KatherineSandys/mini_project_ECE362/inc/f16.h

#ifndef F16
#define F16
const char f16_map[] = {
		0xfe, 0xfe, 0xfe, 0xff, 	/*Color of index 0*/
		  0x12, 0x27, 0xfd, 0xff, 	/*Color of index 1*/
		  0x00, 0x00, 0x01, 0xff, 	/*Color of index 2*/
		  0x03, 0xaa, 0xf9, 0xff, 	/*Color of index 3*/
		  0x09, 0x53, 0xfb, 0xff, 	/*Color of index 4*/
		  0x17, 0x42, 0x4a, 0xff, 	/*Color of index 5*/
		  0x34, 0xfd, 0xfd, 0xff, 	/*Color of index 6*/
		  0x2d, 0xe8, 0xd0, 0xff, 	/*Color of index 7*/
		  0x33, 0xaf, 0x67, 0xff, 	/*Color of index 8*/
		  0xcd, 0x90, 0x04, 0xff, 	/*Color of index 9*/
		  0x71, 0x59, 0x48, 0xff, 	/*Color of index 10*/
		  0xfb, 0x46, 0x02, 0xff, 	/*Color of index 11*/
		  0xa0, 0x01, 0x3c, 0xff, 	/*Color of index 12*/
		  0xad, 0x01, 0x85, 0xff, 	/*Color of index 13*/
		  0xb5, 0xa5, 0xb9, 0xff, 	/*Color of index 14*/
		  0x49, 0x19, 0xa6, 0xff, 	/*Color of index 15*/

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
		};
struct img_descriptor
{
	int width;
	int height;
	int data_size;
};

const struct img_descriptor f16 = {
  .width = 320,
  .height = 240,
  .data_size = 38465
};
#endif
